antmicro/snapdragon-625-baseboard/assets/previews/layer0.png

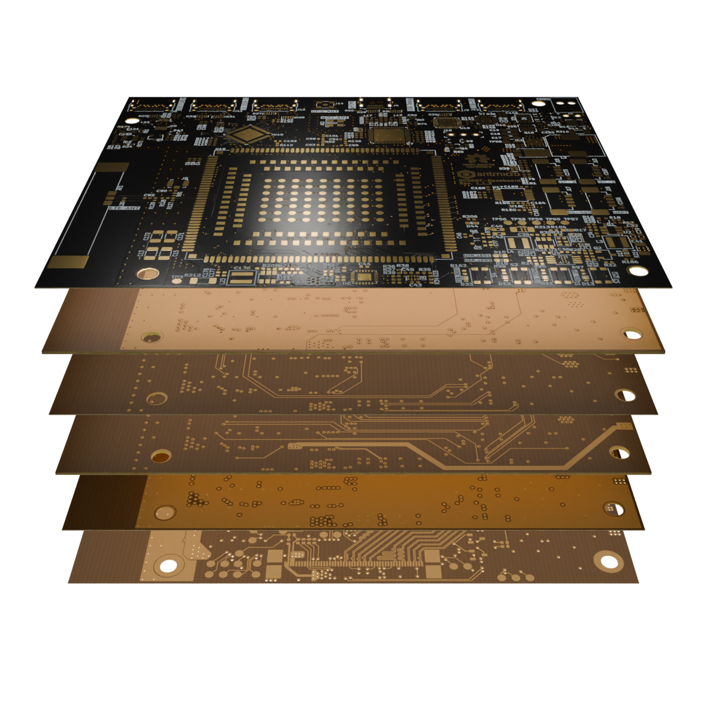
assets/previews/layer0.png
