antmicro/snapdragon-625-baseboard/assets/previews/layer2.png

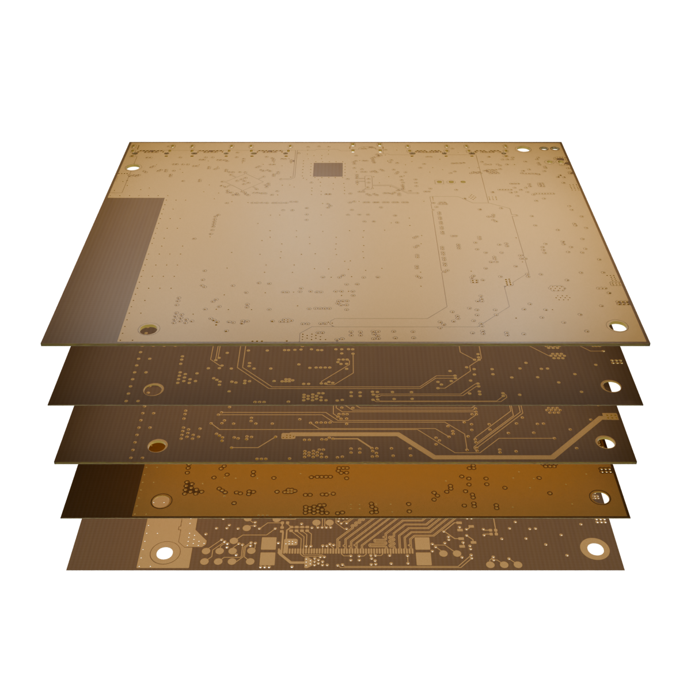
assets/previews/layer2.png
