antmicro/snapdragon-625-baseboard/assets/previews/layer3.png

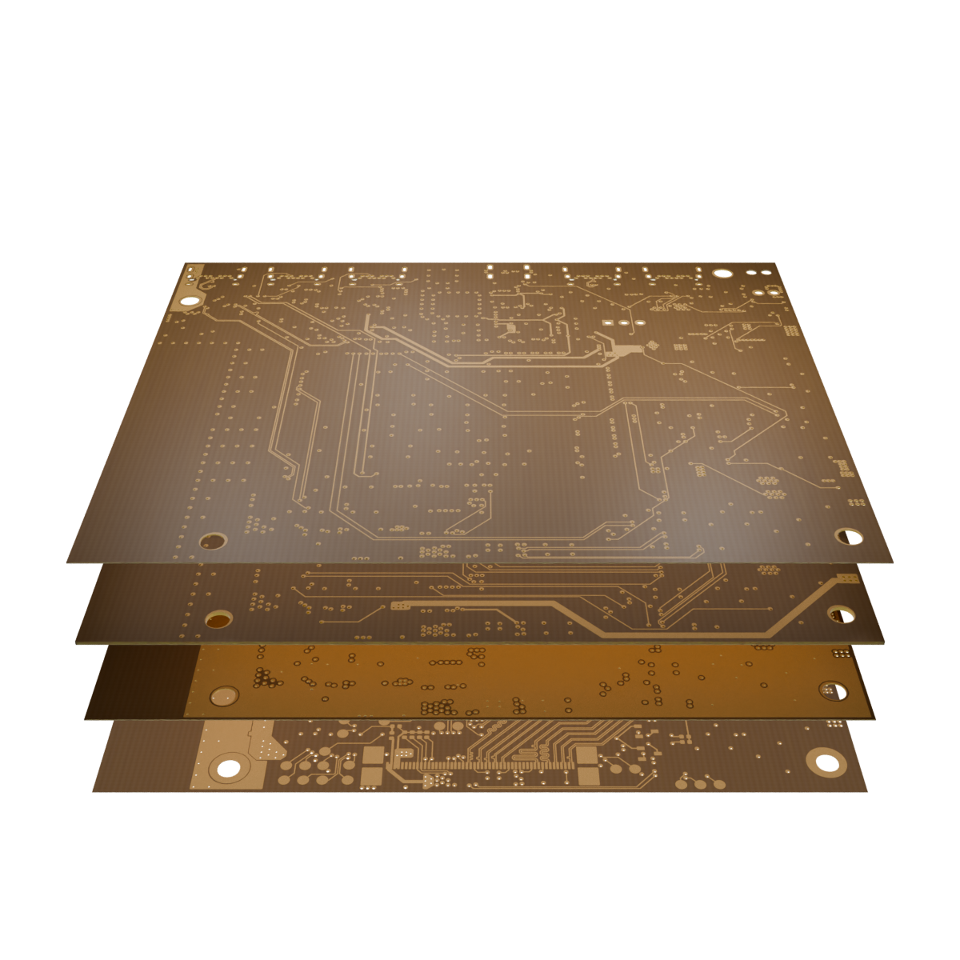
assets/previews/layer3.png
