antmicro/snapdragon-625-baseboard/assets/previews/layer4.png

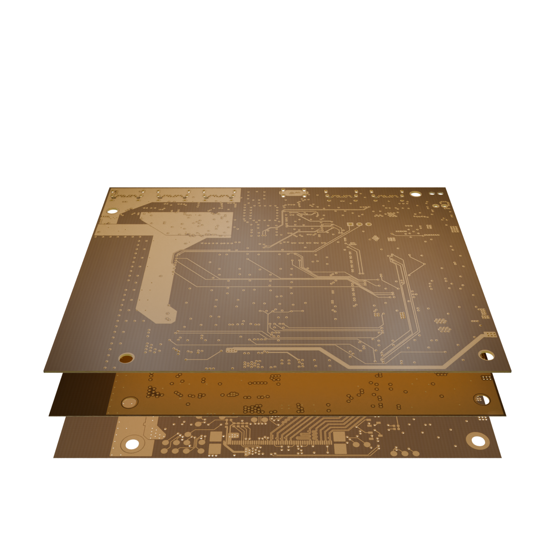
assets/previews/layer4.png
