antmicro/snapdragon-625-baseboard/assets/previews/layer5.png

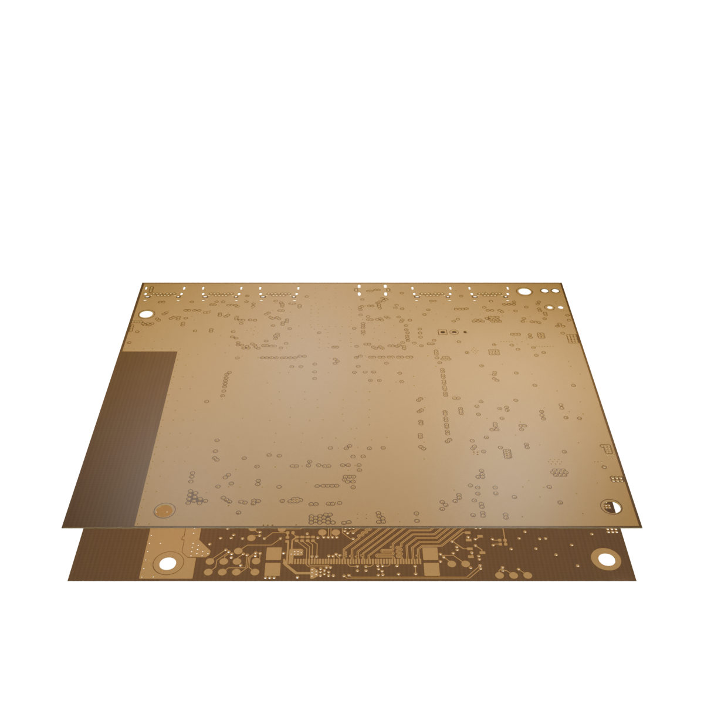
assets/previews/layer5.png
