antmicro/snapdragon-625-baseboard/assets/previews/leftB.png

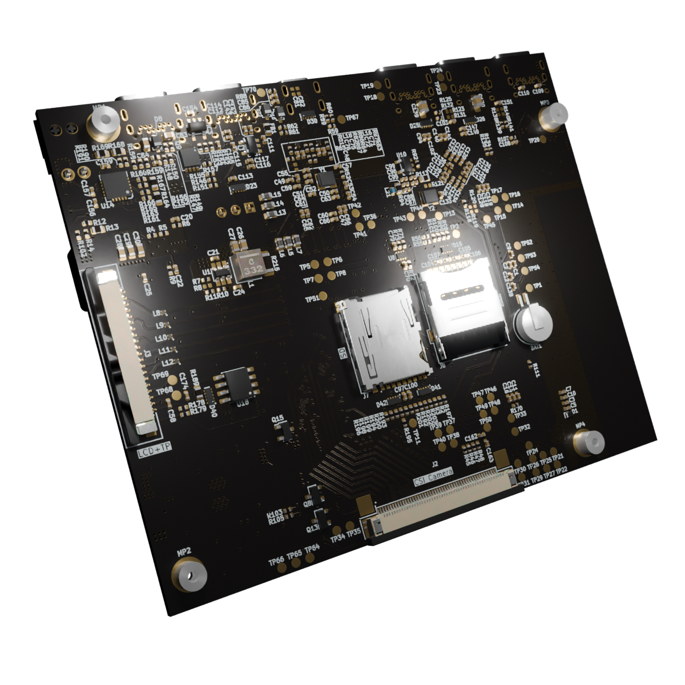
assets/previews/leftB.png
