antmicro/snapdragon-625-baseboard/assets/previews/leftT.png

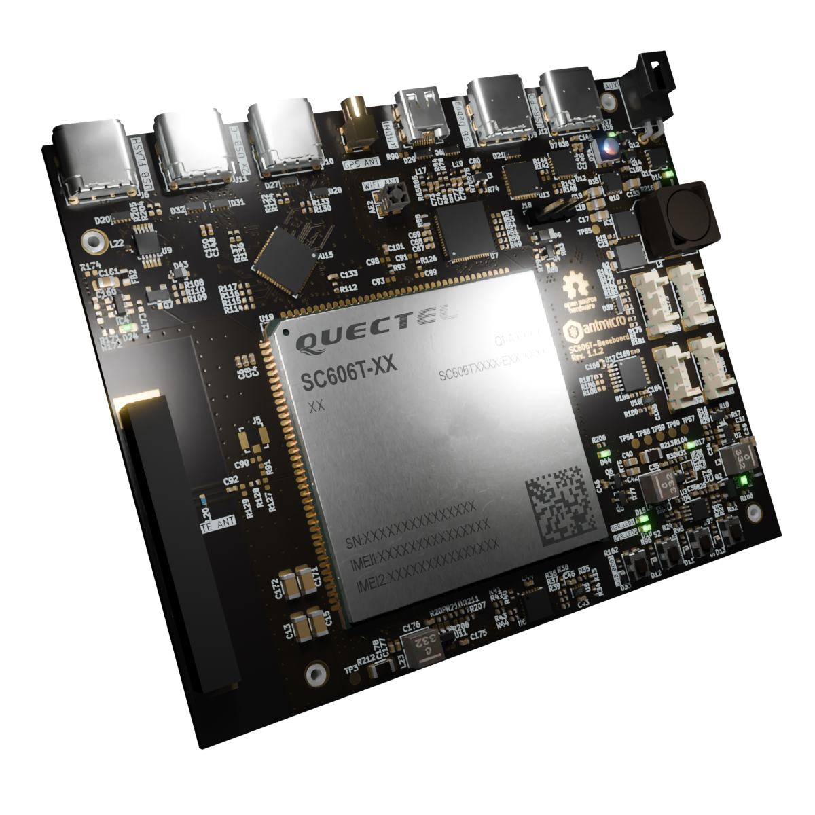
assets/previews/leftT.png
