antmicro/snapdragon-625-baseboard/assets/previews/orthoB.png

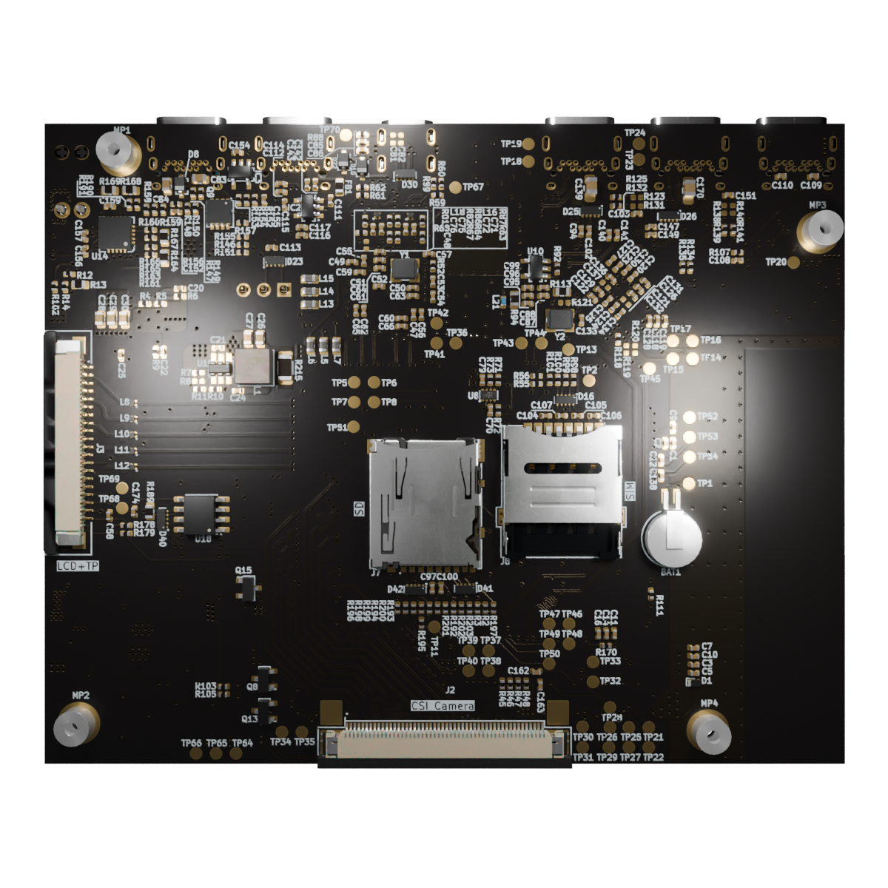
assets/previews/orthoB.png
