antmicro/snapdragon-625-baseboard/assets/previews/orthoT.png

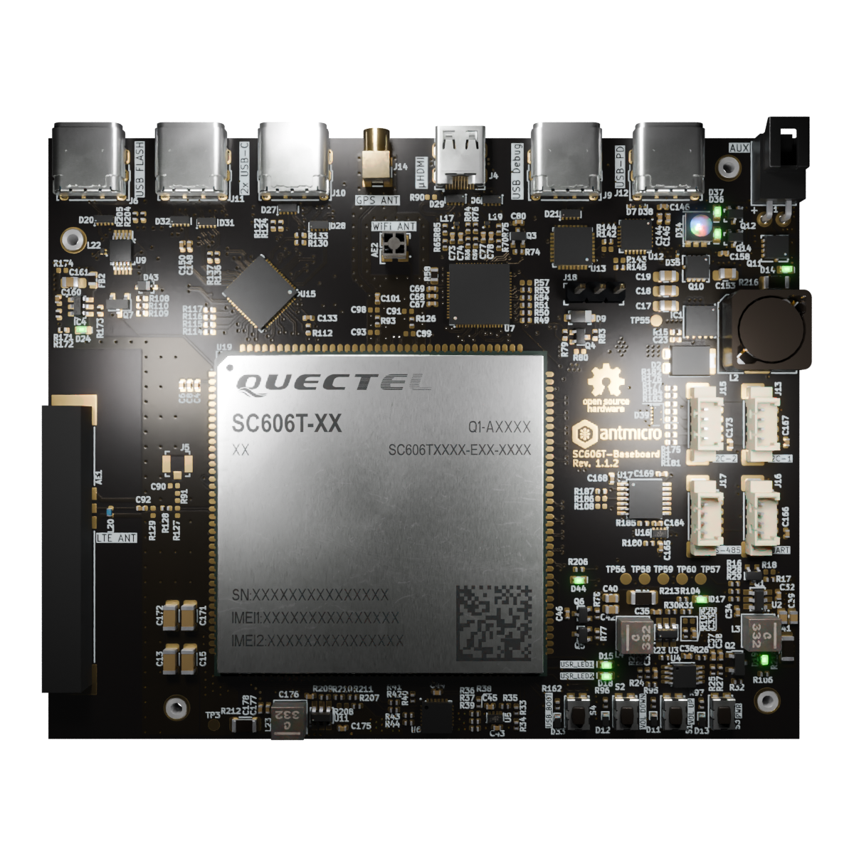
assets/previews/orthoT.png
