antmicro/snapdragon-625-baseboard/assets/previews/rightB.png

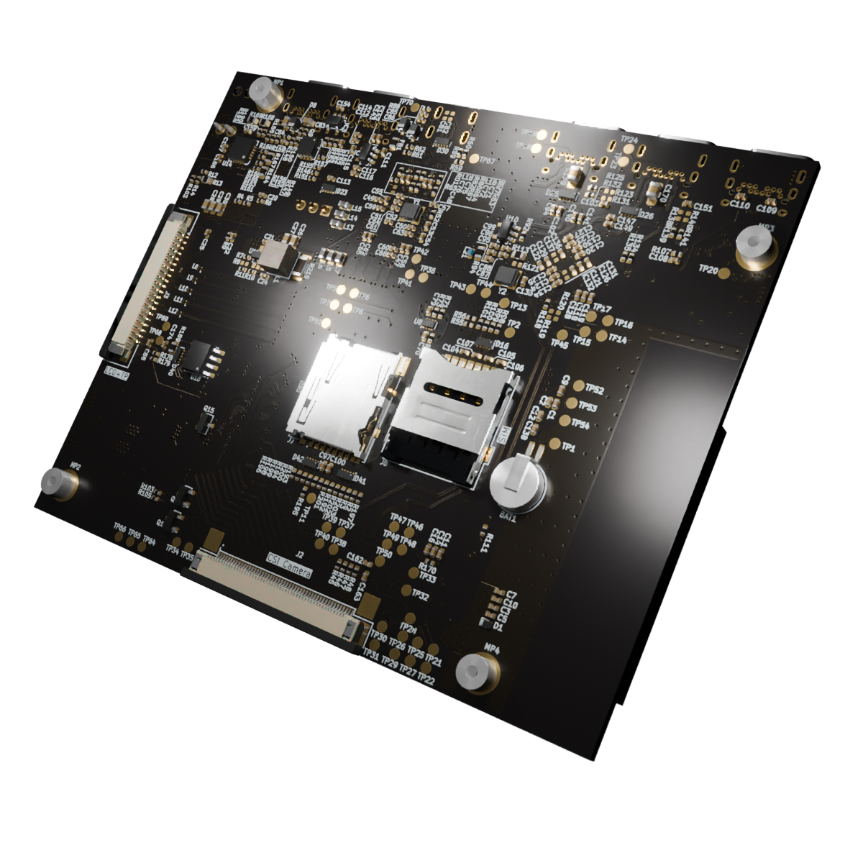
assets/previews/rightB.png
