antmicro/snapdragon-625-baseboard/assets/previews/rightT.png

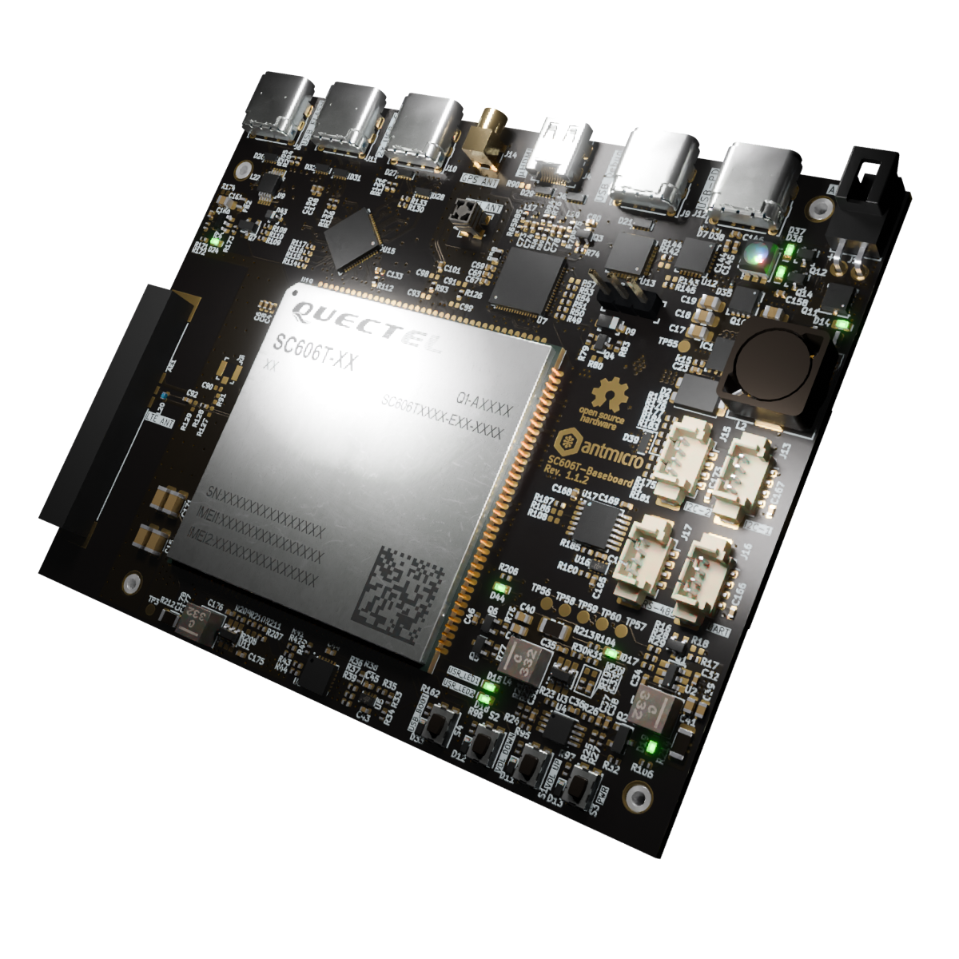
assets/previews/rightT.png
