antmicro/snapdragon-625-baseboard/img/block-diagram.png

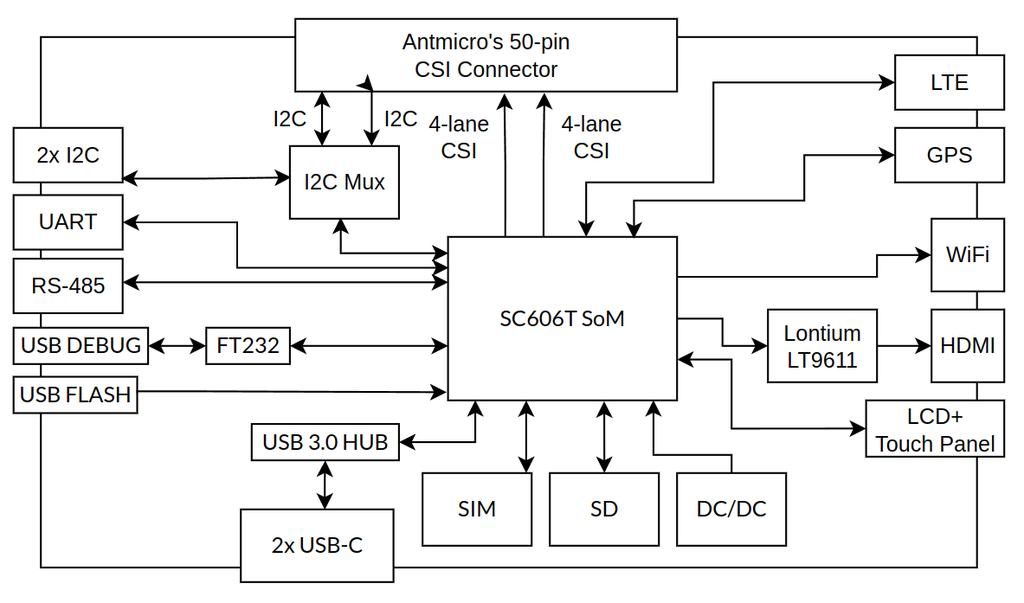
img/block-diagram.png
